LNH-team/dspico-hardware/dspico-artwork-design/guides/high-spec-options.jpg

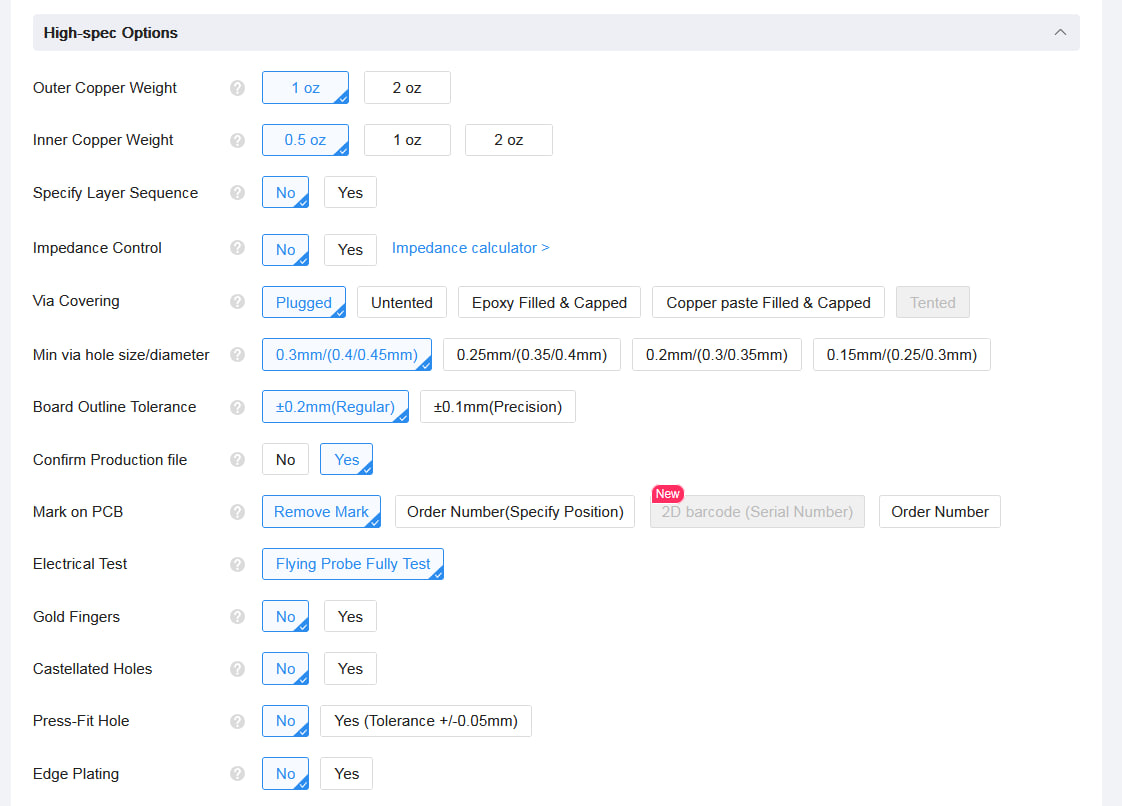
dspico-artwork-design/guides/high-spec-options.jpg
