LNH-team/dspico-hardware/dspico-artwork-design/stickers/dspico-white-sticker.png

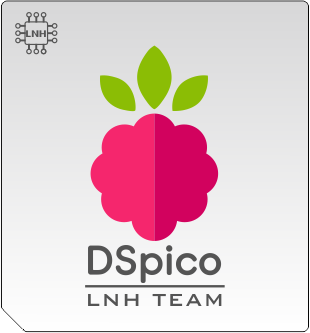
dspico-artwork-design/stickers/dspico-white-sticker.png
